incedius/replicazeron/incStls/brainBox/bottom.stl

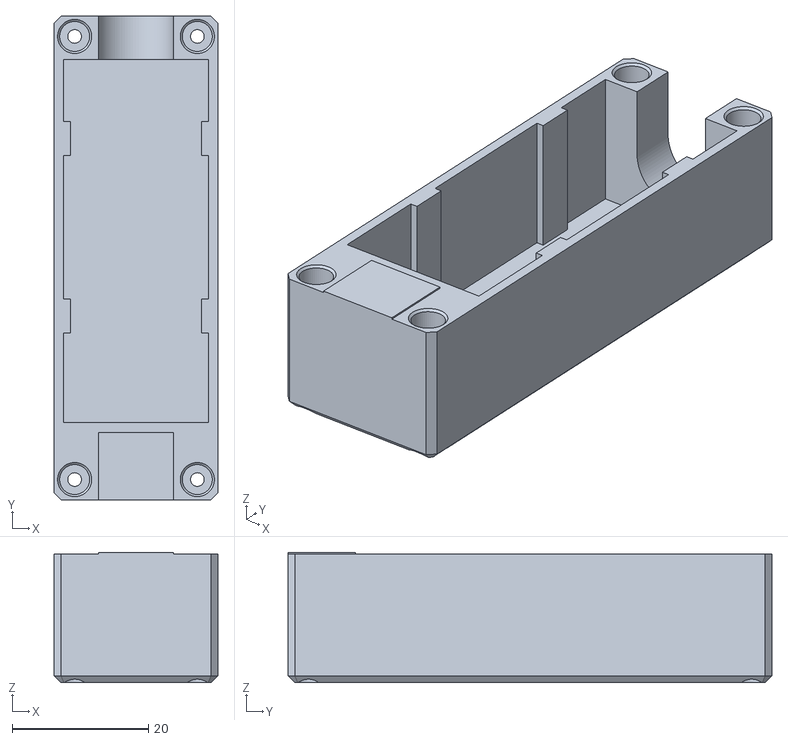
[picture p19: CAD file, 2024-12-31]
incStls/brainBox/bottom.stl
24.0 x 71.0 x 19.1
