incedius/replicazeron/incStls/brainBox/top.stl

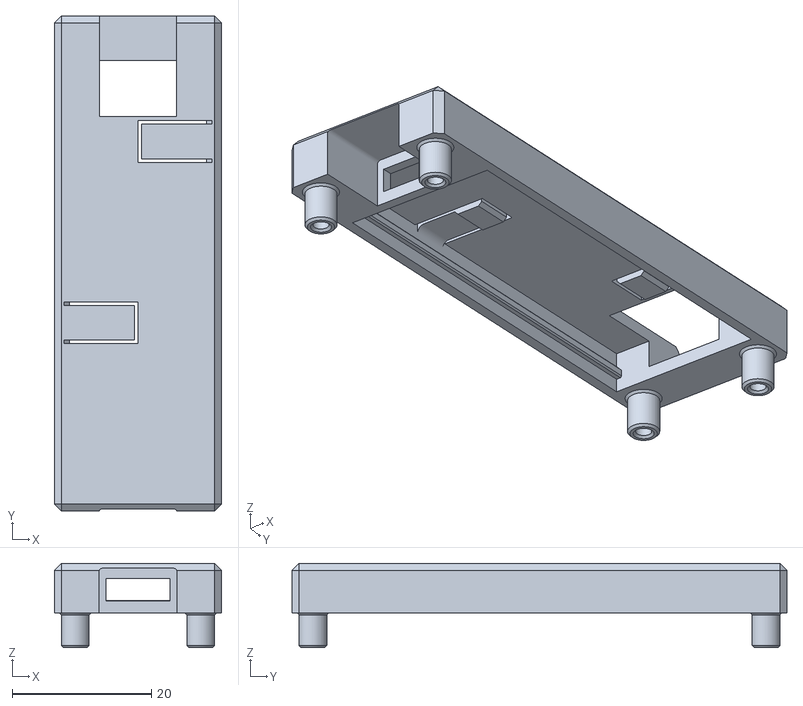
[picture p20: CAD file, 2024-12-31]
incStls/brainBox/top.stl
24.0 x 71.0 x 12.1
