incedius/replicazeron/incStls/replicazeron2/pinkyExtPlus.stl

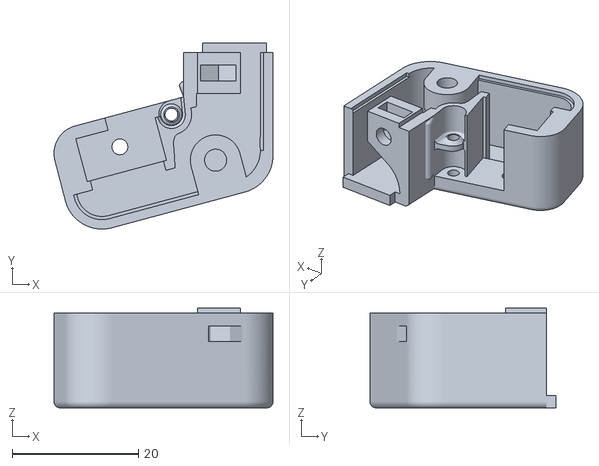
[picture p21: CAD file, 2025-03-29]
incStls/replicazeron2/pinkyExtPlus.stl
34.7 x 29.5 x 15.8
