incedius/replicazeron/incStls/replicazeron2/pedal3.stl

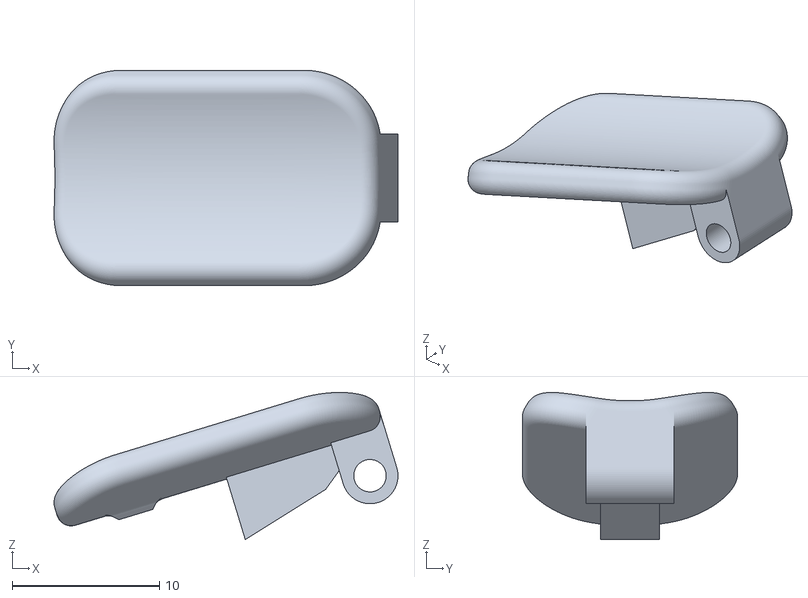
[picture p22: CAD file, 2025-03-29]
incStls/replicazeron2/pedal3.stl
23.3 x 14.6 x 9.98
