incedius/replicazeron/incStls/replicazeron2/towerClip.stl

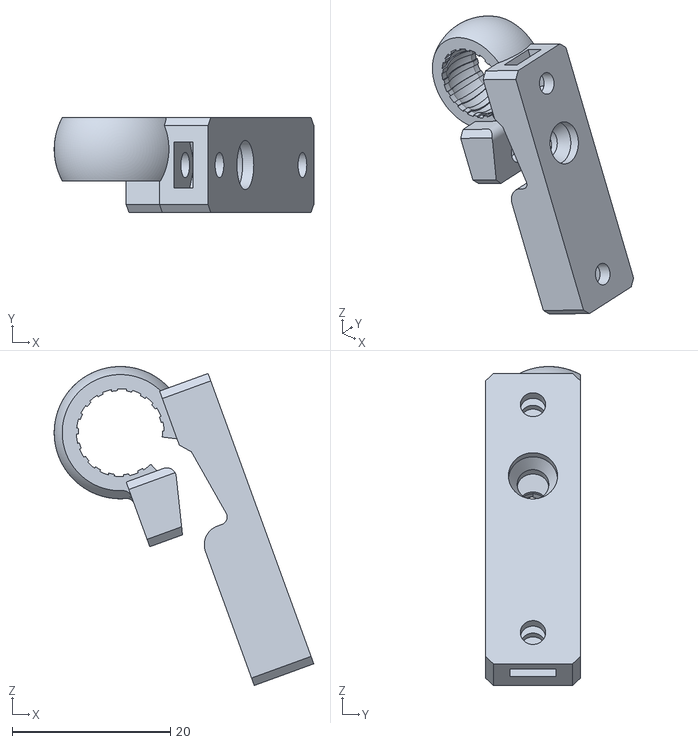
[picture p23: CAD file, 2025-03-29]
incStls/replicazeron2/towerClip.stl
32.8 x 12.0 x 40.3
