incedius/replicazeron/incStls/replicazeron2/pedal-1.stl

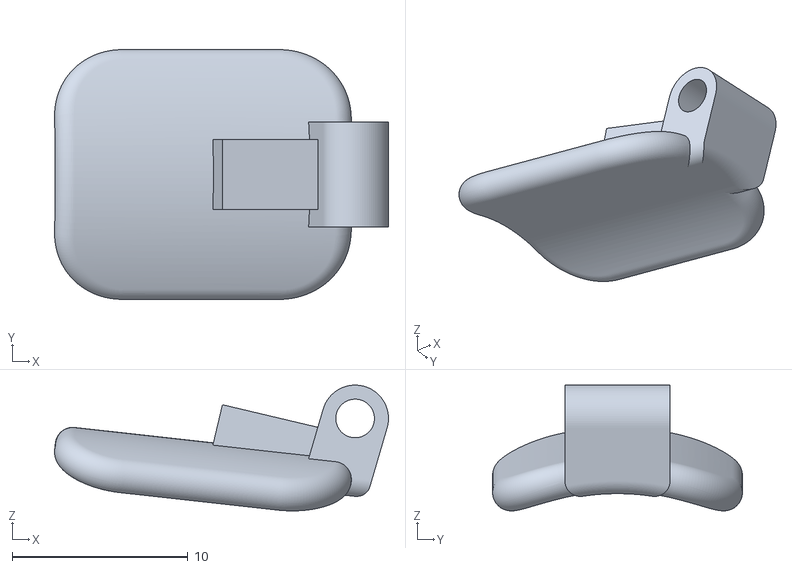
[picture p24: CAD file, 2025-03-29]
incStls/replicazeron2/pedal-1.stl
19.0 x 14.2 x 7.17
