incedius/replicazeron/incStls/replicazeron2/NewTowerPinky.stl

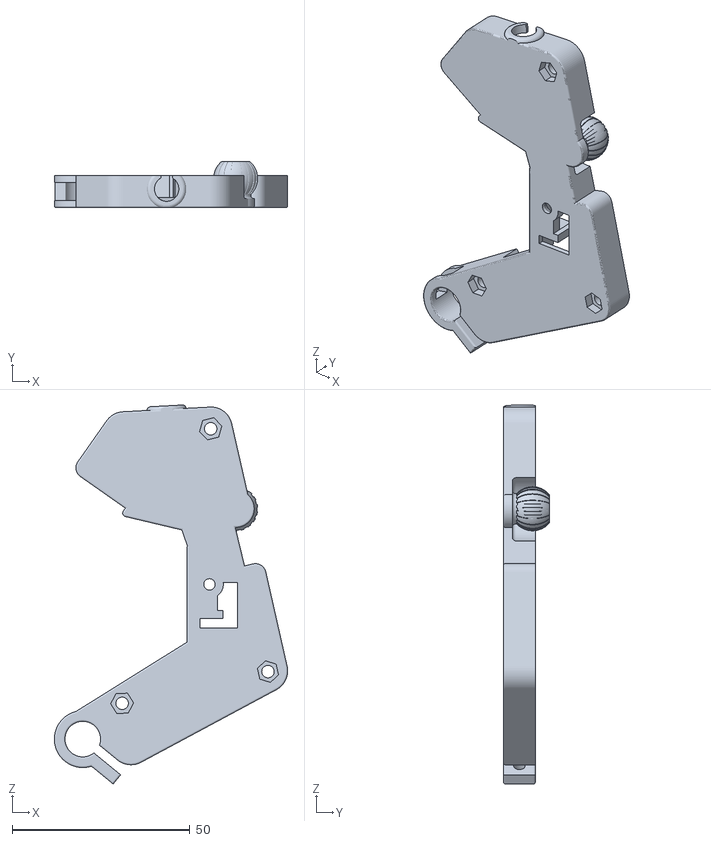
[picture p25: CAD file, 2025-03-29]
incStls/replicazeron2/NewTowerPinky.stl
65.6 x 13.0 x 106.6
