incedius/replicazeron/incStls/replicazeron2/pedal4.stl

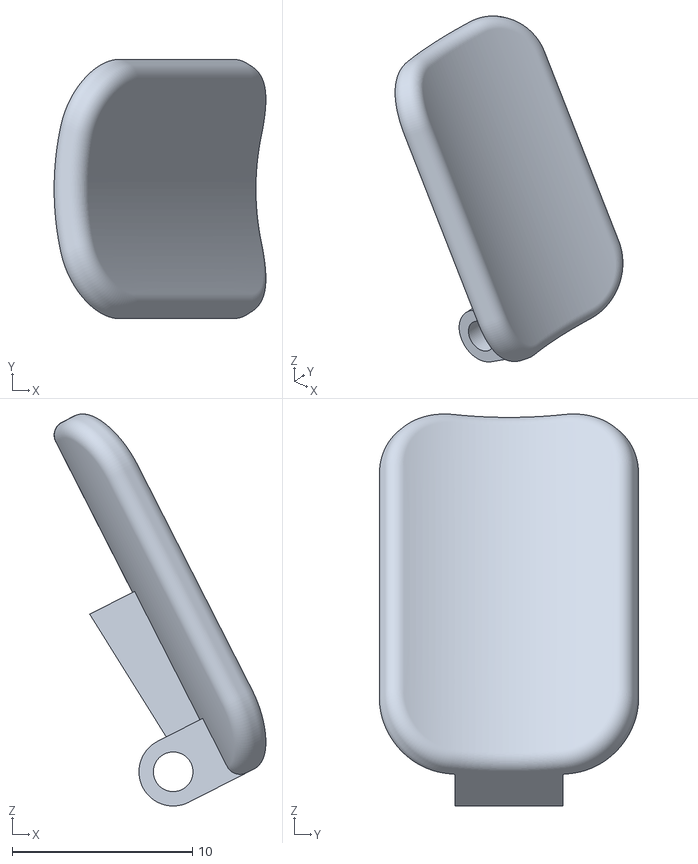
[picture p26: CAD file, 2025-03-29]
incStls/replicazeron2/pedal4.stl
11.8 x 14.4 x 21.8
