incedius/replicazeron/incStls/replicazeron2/NewTowerCover.stl

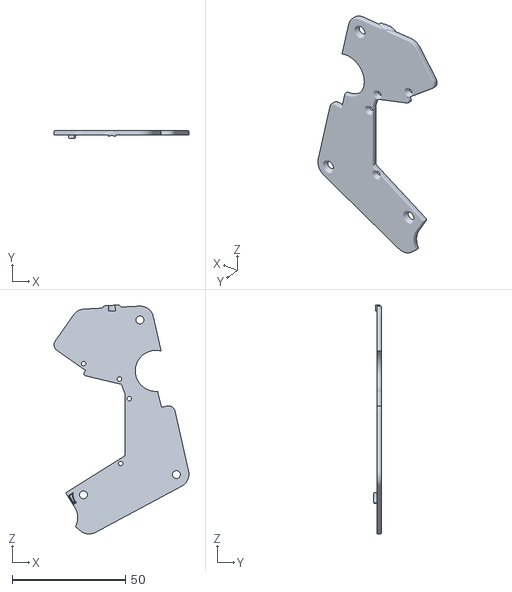
[picture p27: CAD file, 2025-03-29]
incStls/replicazeron2/NewTowerCover.stl
59.5 x 3.50 x 101.1
