incedius/replicazeron/incStls/replicazeron2/pinkyExtPlusCap.stl

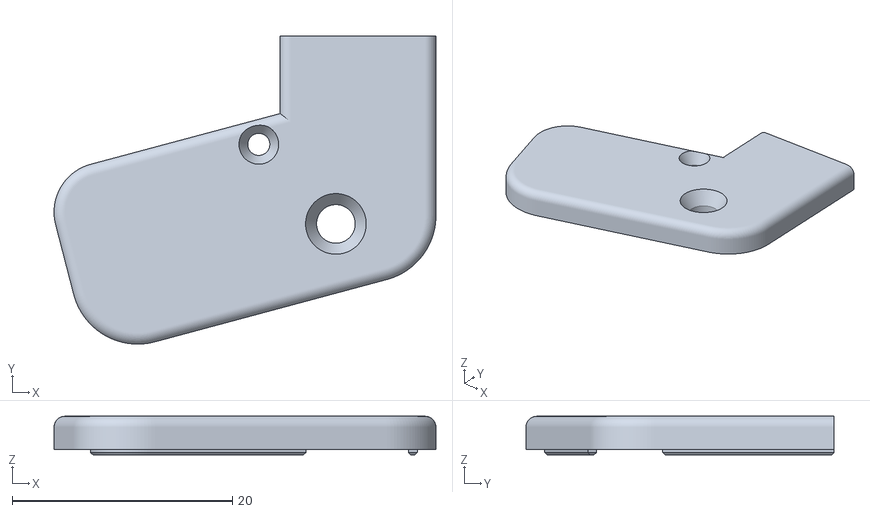
[picture p28: CAD file, 2025-03-29]
incStls/replicazeron2/pinkyExtPlusCap.stl
34.7 x 28.0 x 3.50
