incedius/replicazeron/incStls/replicazeron2/solderGuide.stl

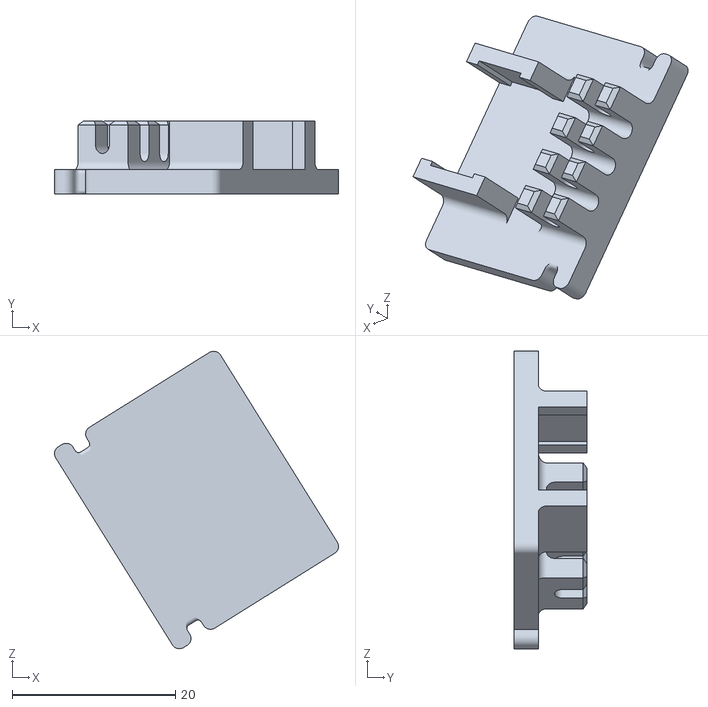
[picture p29: CAD file, 2025-03-29]
incStls/replicazeron2/solderGuide.stl
34.8 x 9.00 x 36.4
