incedius/replicazeron/incStls/replicazeron2/towerSolderGuide.stl

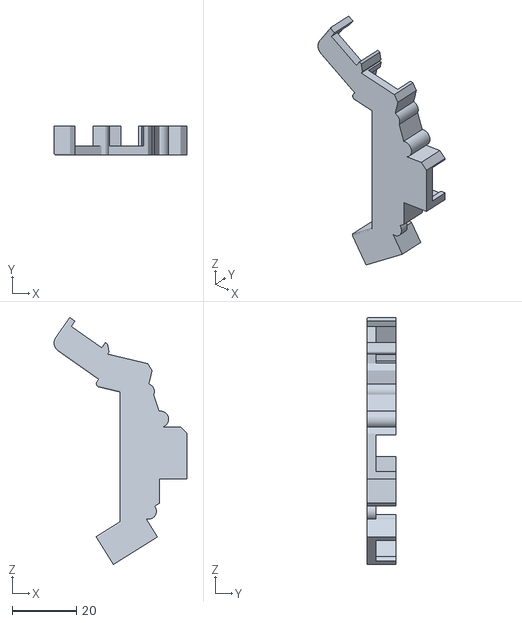
[picture p30: CAD file, 2025-03-29]
incStls/replicazeron2/towerSolderGuide.stl
41.4 x 9.00 x 76.9
