incedius/replicazeron/incStls/replicazeron2/NewTowerPinkyTopless.stl

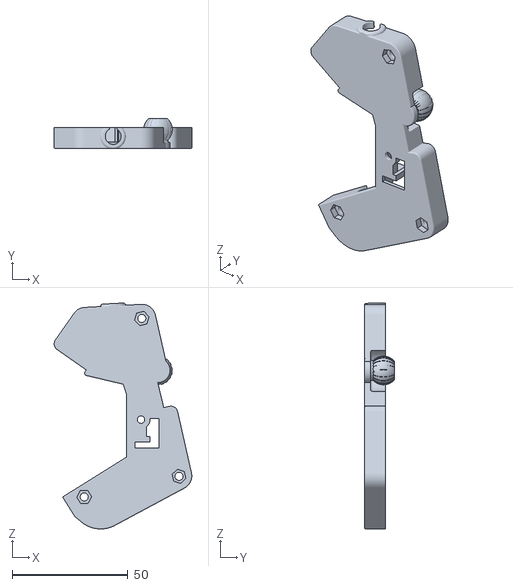
[picture p31: CAD file, 2025-03-29]
incStls/replicazeron2/NewTowerPinkyTopless.stl
59.5 x 13.0 x 97.7
