incedius/replicazeron/incStls/replicazeron2/NewTowerCoverTopless.stl

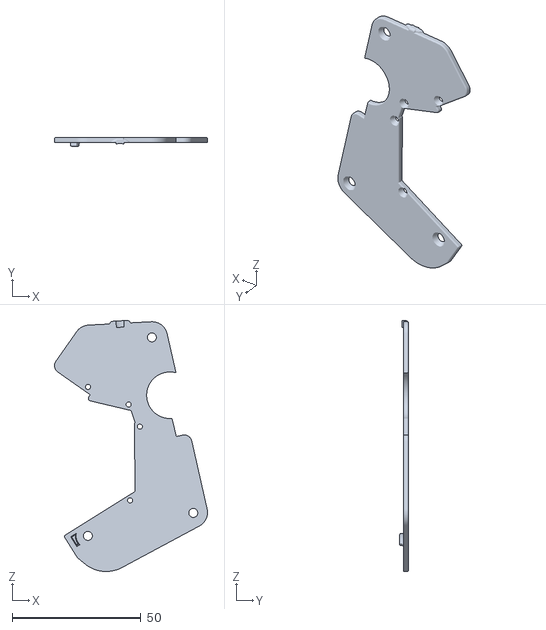
[picture p32: CAD file, 2025-03-29]
incStls/replicazeron2/NewTowerCoverTopless.stl
59.5 x 3.50 x 97.6
