incedius/replicazeron/incStls/replicazeron2/wireGuide.stl

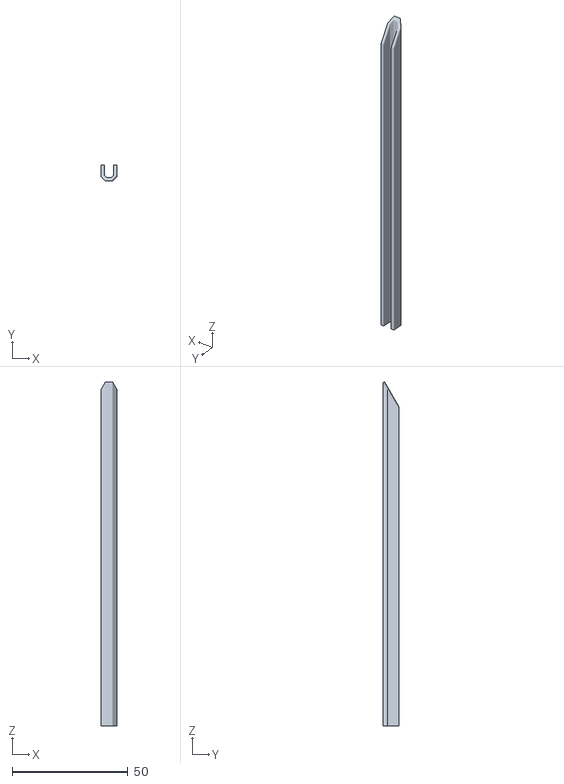
[picture p33: CAD file, 2025-03-29]
incStls/replicazeron2/wireGuide.stl
7.00 x 7.00 x 148.6
